lnadora/ECE411-Team3/Assignment Documentation/Week7 Assignment/autoTempHeater_Change_Heater_state_Level1.drawio.pdf

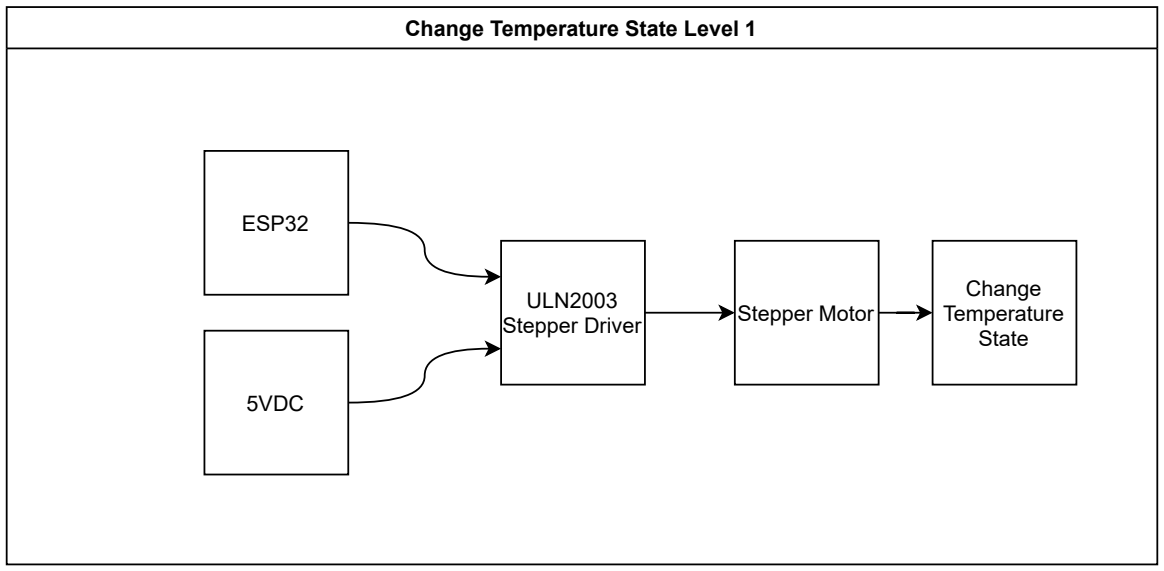
[picture p19: figure]
Change Temperature State Level 1; 5VDC; ESP32; Stepper Motor; Change Temperature State; ULN2003 Stepper Driver
