lnadora/ECE411-Team3/Assignment Documentation/Week7 Assignment/autoTempHeater_OLEDLevel1.drawio.pdf

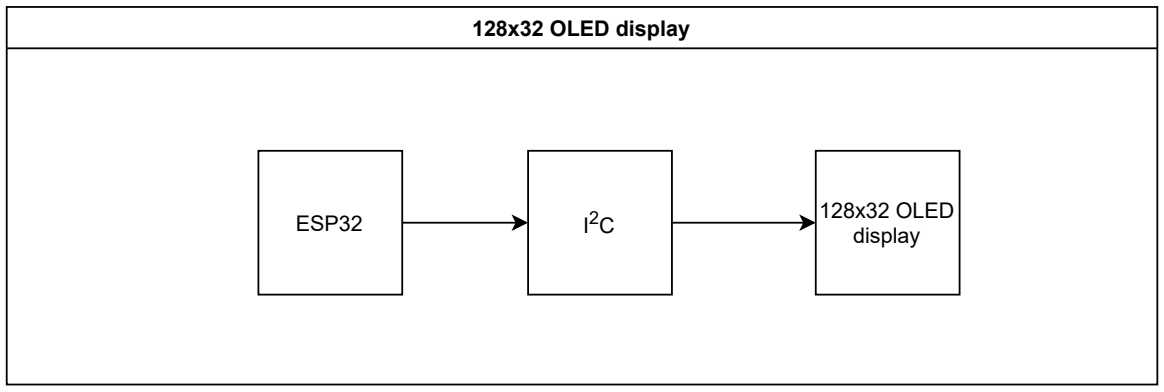
[picture p20: figure]
128x32 OLED display; ESP32
