lnadora/ECE411-Team3/Assignment Documentation/Week7 Assignment/autoTempHeater_TemperatureSensorLevel1.drawio.pdf

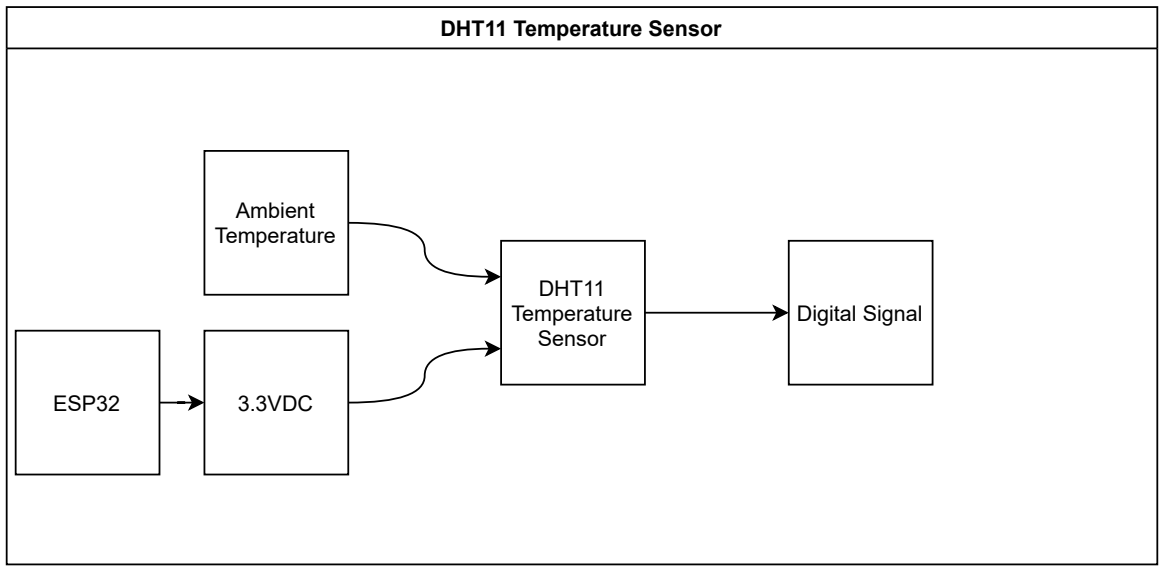
[picture p21: figure]
DHT11 Temperature Sensor; Ambient Temperature; ESP32; 3.3VDC; Digital Signal
