lnadora/ECE411-Team3/Assignment Documentation/Week7 Assignment/autoTempHeater_UserInputLevel1.drawio.pdf

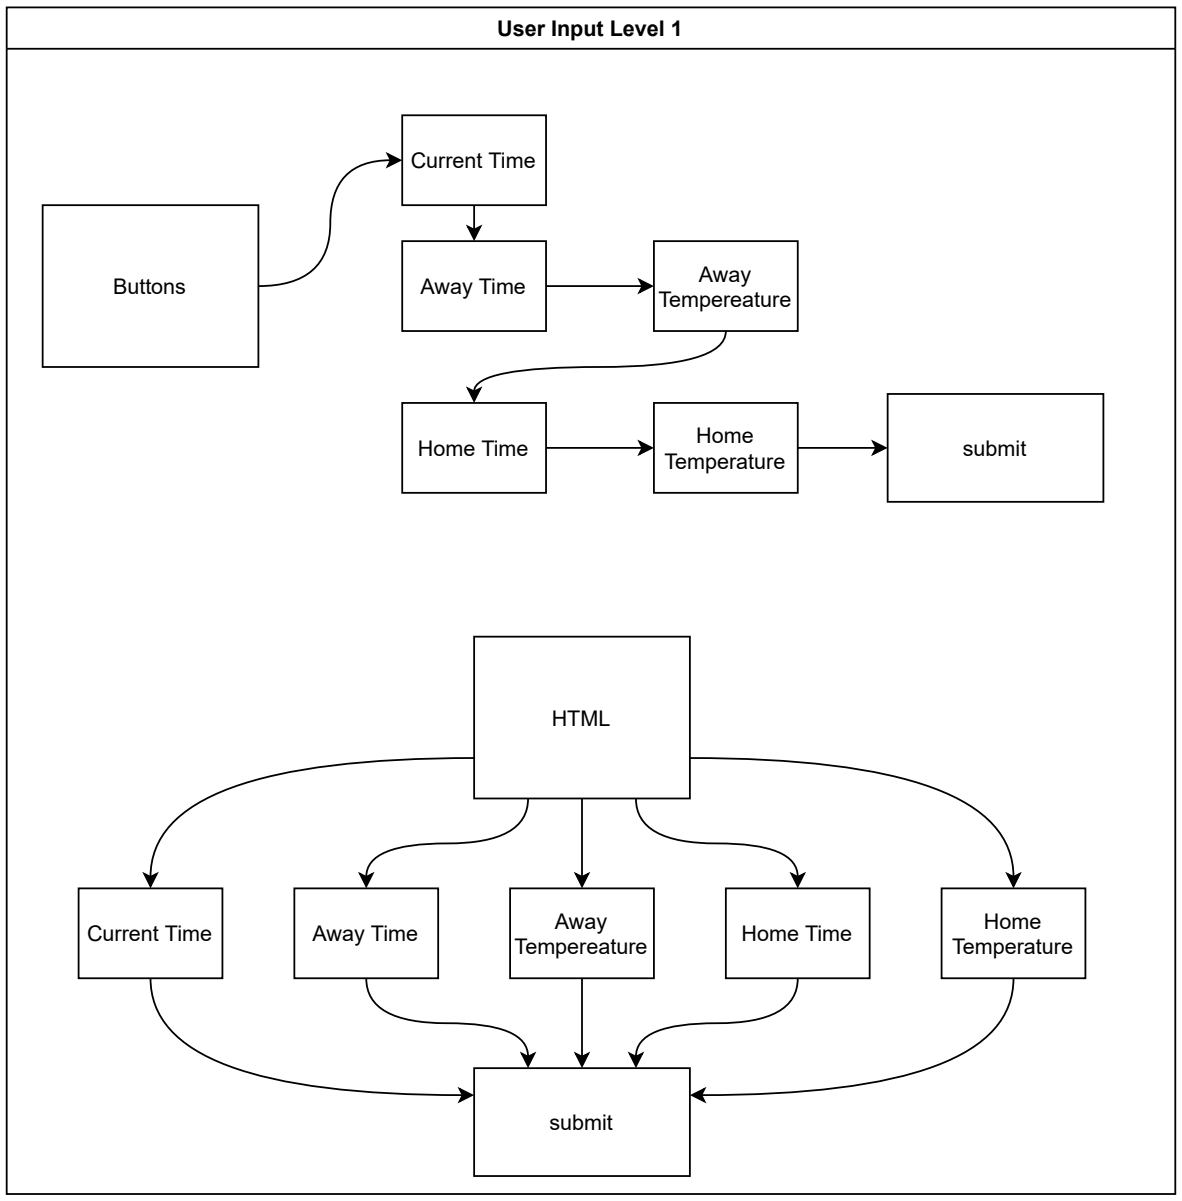
[picture p22: figure]
User Input Level 1; Buttons; Current Time; Away Time; Home Time; Away Tempereature; Home; Temperature; submit; HTML; Home Time Away; Tempereature; Home Temperature
