lnadora/ECE411-Team3/Assignment Documentation/Week6 Assignment/ECE411Team3 project.pdf

## ECE 411 Team 3 Automatic Thermostat

Knob Controller | Nov 4, 2021
2021 Fall | http://
Project manager | Luke Hoskam
Project dates | Oct 24, 2021 - Nov 19, 2021
Completion | 36%
Tasks | 40
Resources | 4

Name | Begin date | End date | Resources
Breadboard Prototype | 10/24/21 | 10/31/21 | Luke Hoskam
Build Prototype | 10/24/21 | 10/27/21 | Luke Hoskam
Code to test the circuit | 10/24/21 | 10/27/21 | Luke Hoskam
Test Prototype | 10/28/21 | 10/31/21 | Luke Hoskam
3d model Case | 11/1/21 | 11/11/21 | Luis Nadora
Gears | 11/1/21 | 11/5/21 | Luis Nadora
Enclosure models prototype v1.0 | 11/1/21 | 11/6/21 | Luis Nadora
Enclosure models prototype v2.0 | 11/7/21 | 11/10/21 | Luis Nadora
Rough Draft of CAD You should be mostly done! Now the only things left are changes for out of stock components, changes from design reviews, changes for DFX, etc.! Submit your KiCAD _pro, _sch, and _pcb files, or PDFs of them if you're not using KiCAD. | 11/7/21 | 11/11/21 | Luke Hoskam, Luis Nadora
Power | 10/31/21 | 11/12/21 | Zheng Zhang
Battery (Not Needed) Decided against this currently because the current drain by the stepper motor trying to stay still is too much | 11/5/21 | 11/8/21 | Zheng Zhang
Battery management system to charge( Not needed) Decided against this currently because the current drain by the stepper motor trying to stay still is too much. | 11/8/21 | 11/12/21 | Zheng Zhang

How much voltage/current used

We found the current draw by the ESP32 with the stepper motor connected to be 0.4A at 5V

10/31/21 | 11/1/21 | Zheng Zhang, Luke Hoskam

voltage regulation

Decided on AMS1117

11/2/21 | 11/5/21 | Zheng Zhang
Website Design | 11/4/21 | 11/14/21 | Luke Hoskam, Kai Han
Learn more about websocket | 11/4/21 | 11/6/21 | Luke Hoskam, Kai Han
Basic web controls | 11/7/21 | 11/9/21 | Luke Hoskam, Kai Han
Temp set contol | 11/10/21 | 11/14/21 | Luke Hoskam, Kai Han
Time leaving (to shut off heater) | 11/10/21 | 11/14/21 | Luke Hoskam, Kai Han
Time arriving(to turn on heater) | 11/10/21 | 11/14/21 | Luke Hoskam, Kai Han
Change icon heating when the heater is on | 11/10/21 | 11/14/21 | Luke Hoskam, Kai Han
Coding Tasks | 11/1/21 | 11/13/21 | Luke Hoskam
Investigate using OLED screens | 11/1/21 | 11/2/21 | Luke Hoskam
Implement OLED screen | 11/3/21 | 11/7/21 | Luke Hoskam
Research Deep Sleep mode on ESP32(maybe) 11/8/21 | 11/8/21 | Luke Hoskam
Implement Deep Sleep (maybe) | 11/9/21 | 11/13/21 | Luke Hoskam
Add Time data from online clocks | 11/1/21 | 11/5/21 | Luke Hoskam

## ECE 411 Team 3 Automatic

Thermostat Knob Controller | Nov 4, 2021
Tasks | 2

Name | Begin date | End date | Resources
Calibrating the max distance of travel | 11/8/21 | 11/11/21 | Luke Hoskam
Bill of Materials | 11/7/21 | 11/11/21 | Zheng Zhang, Luke Hoskam, Luis Nadora, Kai Han
Add price to each component | 11/7/21 | 11/11/21 | Zheng Zhang, Luke Hoskam, Luis Nadora, Kai Han
List each component | 11/7/21 | 11/11/21 | Zheng Zhang, Luke Hoskam, Luis Nadora, Kai Han
Schematic | 10/24/21 | 11/18/21 | Luke Hoskam
Preliminary Schematic | 10/24/21 | 10/28/21 | Luke Hoskam
Updated Schematic | 10/31/21 | 11/4/21 | Luke Hoskam
FAB the Board | 11/15/21 | 11/18/21 | Zheng Zhang, Luke Hoskam, Luis Nadora, Kai Han
Schematic design | 11/1/21 | 11/5/21 | Luke Hoskam
Decide on LEDs | 11/1/21 | 11/5/21 | Luke Hoskam
Add buttons | 11/1/21 | 11/5/21 | Luke Hoskam
Add Power system | 11/4/21 | 11/5/21 | Luke Hoskam

Functional Decomposition

Draw a top-level (Level 0) block diagram of your practicum project showing all inputs and outputs.

Draw a Level 1 block diagram showing the principal components or modules of your project along with the interconnections between them.

For each component or module in the next-level block diagram, create a top-level (Level 0) block diagram of that component or module that describes its functionality, inputs, and outputs.

Consult the lecture slides for proper format for capturing the block diagram and describing inputs and outputs.

Post these to your project wiki and upload to D2L as a single PDF file.

11/7/21 | 11/11/21 | Zheng Zhang, Luke Hoskam, Luis Nadora, Kai Han
Tasks | 3

Name | Default role
Zheng Zhang | developer
Luke Hoskam | project manager
Luis Nadora | developer
Kai Han | developer

## Resources

## Gantt Chart

Name | Begin date | End date | Resources
Breadboard Prototype | 10/24/21 | 10/31/21 | Luke Hoskam
Build Prototype | 10/24/21 | 10/27/21 | Luke Hoskam
Code to test the circuit | 10/24/21 | 10/27/21 | Luke Hoskam
Test Prototype | 10/28/21 | 10/31/21 | Luke Hoskam
3d model Case | 11/1/21 | 11/11/21 | Luis Nadora
Gears | 11/1/21 | 11/5/21 | Luis Nadora
Enclosure models prototype v1.0 | 11/1/21 | 11/6/21 | Luis Nadora
Enclosure models prototype v2.0 | 11/7/21 | 11/10/21 | Luis Nadora
Rough Draft of CAD | 11/7/21 | 11/11/21 | Luke Hoskam,Luis Nadora
Power | 10/31/21 | 11/12/21 | Zheng Zhang
Battery (Not Needed) | 11/5/21 | 11/8/21 | Zheng Zhang
Battery management system to charge( Not needed) | 11/8/21 | 11/12/21 | Zheng Zhang
How much voltage/current used | 10/31/21 | 11/1/21 | Zheng Zhang,Luke Hoskam
voltage regulation | 11/2/21 | 11/5/21 | Zheng Zhang
Website Design | 11/4/21 | 11/14/21 | Luke Hoskam,Kai Han
Learn more about websocket | 11/4/21 | 11/6/21 | Luke Hoskam,Kai Han
Basic web controls | 11/7/21 | 11/9/21 | Luke Hoskam,Kai Han
Temp set contol | 11/10/21 | 11/14/21 | Luke Hoskam,Kai Han
Time leaving (to shut off heater) | 11/10/21 | 11/14/21 | Luke Hoskam,Kai Han
Time arriving(to turn on heater) | 11/10/21 | 11/14/21 | Luke Hoskam,Kai Han
Change icon heating when the heater is on | 11/10/21 | 11/14/21 | Luke Hoskam,Kai Han
Coding Tasks | 11/1/21 | 11/13/21 | Luke Hoskam
Investigate using OLED screens | 11/1/21 | 11/2/21 | Luke Hoskam
Implement OLED screen | 11/3/21 | 11/7/21 | Luke Hoskam
Research Deep Sleep mode on ESP32(maybe) | 11/8/21 | 11/8/21 | Luke Hoskam
Implement Deep Sleep (maybe) | 11/9/21 | 11/13/21 | Luke Hoskam
Add Time data from online clocks | 11/1/21 | 11/5/21 | Luke Hoskam
Calibrating the max distance of travel | 11/8/21 | 11/11/21 | Luke Hoskam
Bill of Materials | 11/7/21 | 11/11/21 | Zheng Zhang,Luke Hoskam...
Add price to each component | 11/7/21 | 11/11/21 | Zheng Zhang,Luke Hoskam...
List each component | 11/7/21 | 11/11/21 | Zheng Zhang,Luke Hoskam...
Schematic | 10/24/21 | 11/18/21 | Luke Hoskam
Preliminary Schematic | 10/24/21 | 10/28/21 | Luke Hoskam
Updated Schematic | 10/31/21 | 11/4/21 | Luke Hoskam
FAB the Board | 11/15/21 | 11/18/21 | Zheng Zhang,Luke Hoskam...
Schematic design | 11/1/21 | 11/5/21 | Luke Hoskam
Decide on LEDs | 11/1/21 | 11/5/21 | Luke Hoskam
Add buttons | 11/1/21 | 11/5/21 | Luke Hoskam
Add Power system | 11/4/21 | 11/5/21 | Luke Hoskam
Functional Decomposition | 11/7/21 | 11/11/21 | Zheng Zhang,Luke Hoskam...
October 2021 | November 2021 | December 2021
22 | 23 | 24 | 25 | 26 | 27 | 28 | 29 | 30 | 31

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
9 | 10 | 11 | 12 | 13 | 14 | 15 | 16 | 17 | 18 | 19 | 20 | 21 | 22 | 23 | 24 | 25 | 26 | 27 | 28 | 29 | 30

1

2

Updated Schematic

## Resources Chart

Name | Default role
| Zheng Zhang | developer | 200% 300% 200% 600% 700% 600% 200%
| Luke Hoskam | project man... | 500% 400% 300% 500% 900% 800% 800% 1100% 1000% 500% 1000% 1100% 1100% 1400% 800% 600% 200%
Luis Nadora | developer
Kai Han | developer
300% | 200% | 700% | 600%
200% | 600% | 900% | 500%
October 2021 | November 2021 | December 2021
22 | 23 | 24 | 25 | 26 | 27 | 28 | 29 | 30 | 31

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
9 | 10 | 11 | 12 | 13 | 14 | 15 | 16 | 17 | 18 | 19 | 20 | 21 | 22 | 23 | 24 | 25 | 26 | 27 | 28 | 29 | 30

1

2
