lnadora/ECE411-Team3/Assignment Documentation/Week7 Assignment/autoTempHeater_Level0.drawio.pdf

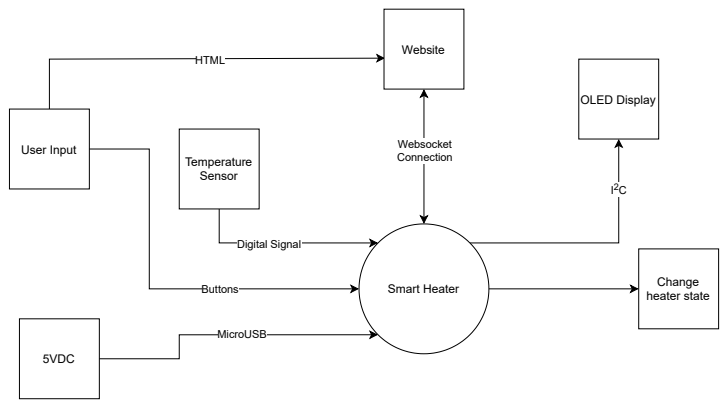
[picture p27: page 1]
Digital Signal; Buttons; MicroUSB; HTML; Websocket Connection; OLED Display; Website; User Input; Temperature Sensor; 5VDC; Smart Heater; Change; heater state
